perry-amsterdam/led-clock/src/ledclock-freertos/task_render.cpp

#include <Arduino.h>
#include "rtos.h"
#include <Adafruit_NeoPixel.h>
#include "net_time.h"
#include "ledhw.h"
#include <time.h>
#include "hal_time_freertos.h"
#include <theme.h>
#include <theme_manager.h>

extern std::atomic<bool> gPowerSaveMode;

void task_render(void*)
{
	vTaskDelay(pdMS_TO_TICKS(50));
	LOG_STACK_WATERMARK("render:init");

	bool ps = gPowerSaveMode.load();
	Serial.printf("PowerSaveMode = %s\n", ps ? "true" : "false");

	EventBits_t bits = xEventGroupGetBits(g_sysEvents);
	while (!(bits & EVT_TIME_READY))
	{
		if (bits & EVT_PORTAL_ON)
		{
			// Captive portal actief  rood pulse
			themeShowStatus(ThemeStatus::PortalActive);
		}
		else if (!(bits & EVT_WIFI_UP))
		{
			// WiFi is niet verbonden  blauw pulse
			themeShowStatus(ThemeStatus::WifiNotConnected);
		}
		else if (!(bits & EVT_TIME_READY))
		{
			// WiFi verbonden, maar tijd nog niet gesynchroniseerd  groen pulse
			themeShowStatus(ThemeStatus::TimeNotReady);
		}

		hal_delay_ms(500);
		bits = xEventGroupGetBits(g_sysEvents);
	}

	for(;;)
	{
		if (isPowerSaveMode())
		{
			ledhwClearAll();
			ledhwShow();
			vTaskDelay(pdMS_TO_TICKS(1000));
			continue;
		}

		LOG_STACK_WATERMARK("render:loop");
		struct tm now;
		time_t epoch = time(nullptr);
		if (getLocalTime(&now))
		{
			#if DEBUG_TIMING
			unsigned long start = micros();
			#endif

			themeUpdate(now, epoch);

			#if DEBUG_TIMING
			unsigned long duration = micros() - start;
			Serial.printf("ws2812bUpdate took %.3f ms\n", duration / 1000.0);
			#endif
		}

		// Render delay.
		vTaskDelay(pdMS_TO_TICKS(themeFrameDelayMs()));
	}
}
