perry-amsterdam/led-clock/src/ledclock-freertos/http_portal.h

#pragma once
#include "globals.h"

String htmlWrap(const String& inner);
void handleRoot();
void handleSave();
void handleReset();
void handleScan();
bool isIpLike(const String& host);
void handleNotFound();
void startPortal();
void stopPortal();
void handlePing();
void startPortalTask();
void stopPortalTask();
